studentkittens/eulenfunk/docs/paper/header.tex

\usepackage[autostyle=true,german=quotes]{csquotes}
\usepackage{graphicx}
\usepackage{lmodern}
\usepackage{hyperref}
\usepackage[utf8]{luainputenc}
\usepackage[T1]{fontenc}
\usepackage{gentium}
\usepackage{eurosym}
%\usepackage{pdfpages}
\pagenumbering{roman} 
\RequirePackage{ccicons}

\usepackage{inconsolata}
\usepackage{fancyhdr}
\usepackage{color}
\usepackage{amssymb}
\usepackage{wasysym}
%\definecolor{titlepagefontcolor}{RGB}{47, 90, 130} 
\definecolor{titlepagefontcolor}{RGB}{216,96,96}
\definecolor{titlepagefontcolorreset}{RGB}{255,255,255}
%\definecolor{titlepagecolor}{RGB}{55, 127, 161} 
%\definecolor{titlepagefontcolor}{RGB}{245,245,245} %Solarized light default text 
%\definecolor{titlepagefontcolor}{RGB}{55, 127, 161} 
%\definecolor{titlepagecolor}{RGB}{245,245,245} %Solarized light default text 
\definecolor{titlepagecolor}{RGB}{252,246,222}
\usepackage{ifthen}
\usepackage[usenames,dvipsnames]{xcolor}
\usepackage[
  paper=a4paper,
  left=30mm,
  right=25mm,
  top=25mm,
  bottom=25mm,
  includefoot,
  foot=\baselineskip,
  bindingoffset=0mm]{geometry}

\usepackage{setspace}
\onehalfspacing 

\usepackage{amssymb}% http://ctan.org/pkg/amssymb
\usepackage{pifont}% http://ctan.org/pkg/pifont
\newcommand{\cmark}{\textcolor{ForestGreen}{\ding{51}}}%
\newcommand{\xmark}{\textcolor{red}{\ding{55}}}%

\hypersetup{colorlinks,breaklinks,urlcolor=titlepagefontcolor,linkcolor=titlepagefontcolor}

\definecolor{gray75}{gray}{0.55}
\newcommand{\hsp}{\hspace{5pt}}

\usepackage{calc}
\usepackage{etoolbox}

\appto\chapterheadstartvskip{%
  \vspace{-7.7em} % Pull up chapter a bit.
  \smash{\makebox[0pt]{%
    \textcolor{titlepagefontcolor}{%
      \usesizeofkomafont{chapter}\rule[-2\ht\strutbox-\dp\strutbox]{2\paperwidth}{1.65\baselineskip}%
}}}}
\renewcommand\chapterformat{%
  \makebox[0pt][r]{\thechapter\ \ \textcolor{white}{\smash{\rule[-2\dp\strutbox]{2.5pt}{2.25\baselineskip}}}}%
  \enskip%
}

\addtokomafont{disposition}{\rmfamily}
\addtokomafont{chapter}{\color{titlepagecolor}}
\addtokomafont{section}{\color{titlepagefontcolor}}
\addtokomafont{subsection}{\color{titlepagefontcolor}}
\addtokomafont{subsubsection}{\color{titlepagefontcolor}}

\renewcommand{\labelitemi}{\textcolor{titlepagefontcolor}{$$$\blacktriangleright$}}
% \renewcommand{\labelitemii}{$\cdot$}
% \renewcommand{\labelitemiii}{$\diamond$}
% \renewcommand{\labelitemiv}{$\ast$}

\pagestyle{fancy}               

\newcommand{\prettypage}{%
    \scshape{~\thepage~~~}
}%

% Configure footer and header
\fancyfoot[C]{%
    % EasterEgg
    \ifthenelse{\value{page}=42}{%
        % Horizontal and vertical flip
        \reflectbox{\scalebox{1}[-1]{\prettypage}}
    }{%
        \ifthenelse{\value{page}=23}{%
            % Horizontal flip
            \reflectbox{\prettypage}
        }{%
            \prettypage
        }%
    }%
}%

% Remove the header from pages with chapters on them:
\fancypagestyle{plain}{%
    \fancyhead{}
    \renewcommand{\headrule}{}
}%

% \setlength{\headheight}{24pt} 

% Comment out for normal twoside:
% \newcommand{\ONESIDEFAKE}

\ifdefined\ONESIDEFAKE
    \fancyhead[L]{{\nouppercase{\slshape{\leftmark}}}}
    \fancyhead[R]{{\nouppercase{\scshape{\rightmark}}}}
\else
    \fancyhead[LO]{{\nouppercase{\slshape{\leftmark}}}}
    \fancyhead[RO]{{\nouppercase{\scshape{\rightmark}}}}
    \fancyhead[LE]{{\nouppercase{\scshape{\rightmark}}}}
    \fancyhead[RE]{{\nouppercase{\slshape{\leftmark}}}}
\fi

%\setlength{\topmargin}{-.5in}  %{-.5625in}
\setlength{\footskip}{25pt} % to put page number 3/4" from the bottom of the page (1/4" from bottom of body text)
%\setlength{\textheight}{9in}
%\setlength{\textwidth}{6in}
\usepackage[
    type={CC},
    modifier={by-nc-sa},
    version={3.0},
]{doclicense}
