studentkittens/eulenfunk/docs/paper/images/about.png

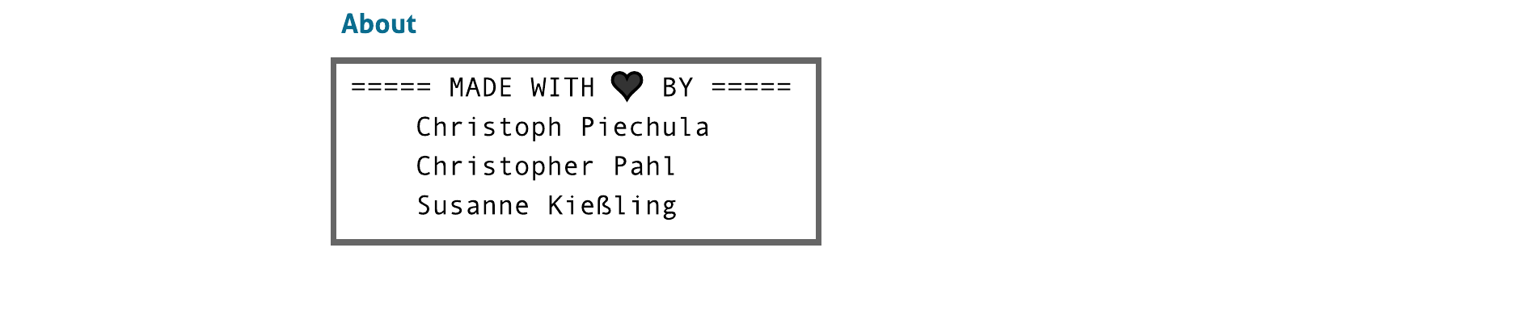
docs/paper/images/about.png
