studentkittens/eulenfunk/docs/paper/images/back_1.png

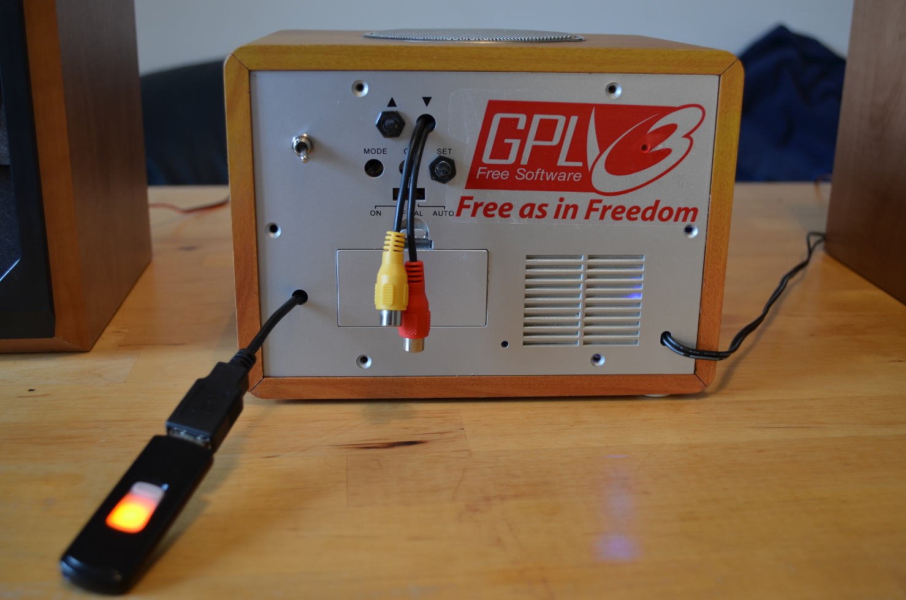
docs/paper/images/back_1.png
