studentkittens/eulenfunk/docs/paper/images/clock.png

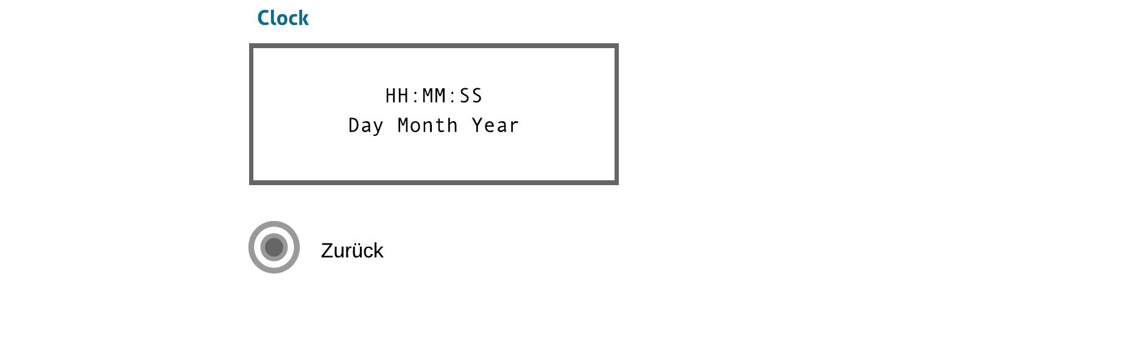
docs/paper/images/clock.png
