studentkittens/eulenfunk/docs/paper/images/currentsong.png

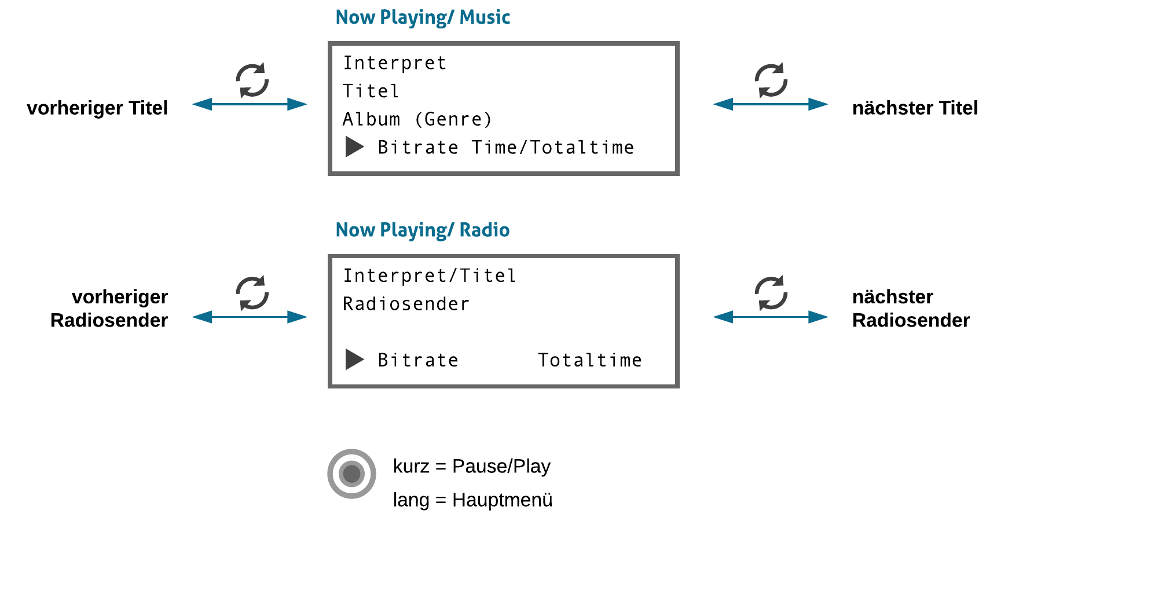
docs/paper/images/currentsong.png
