studentkittens/eulenfunk/docs/paper/images/encoding.png

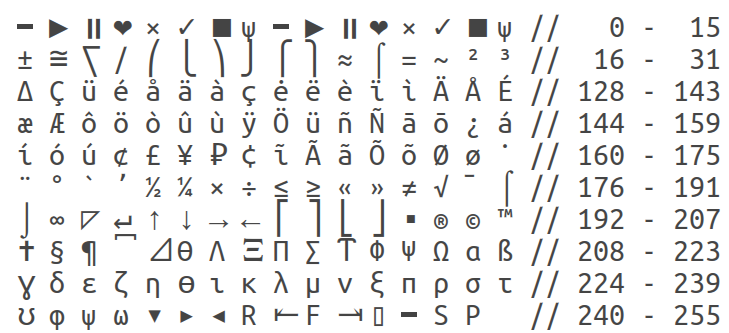
docs/paper/images/encoding.png
