studentkittens/eulenfunk/docs/paper/images/eulenfunk-ambilight.png

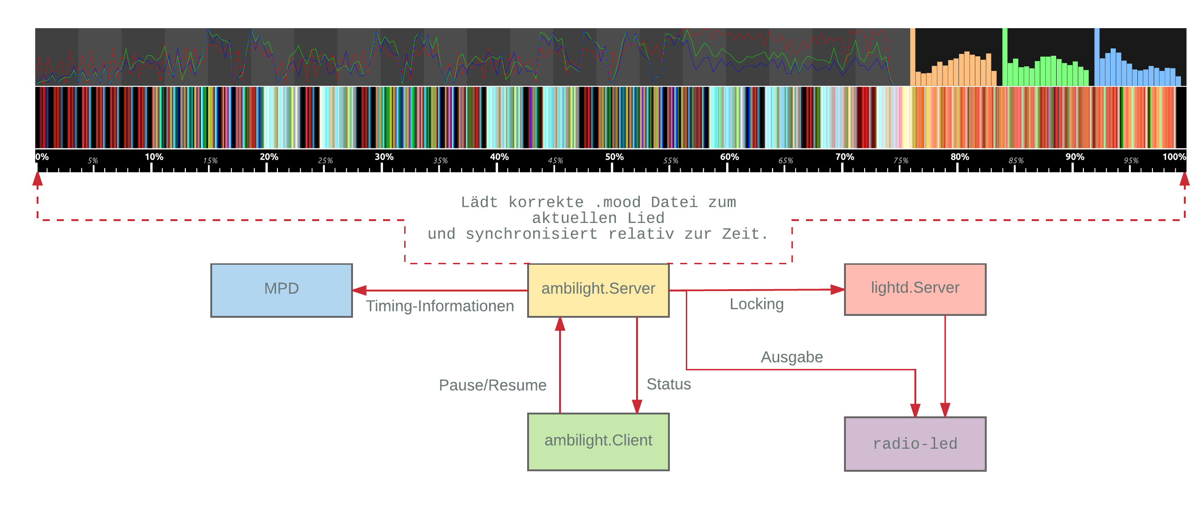
docs/paper/images/eulenfunk-ambilight.png
