studentkittens/eulenfunk/docs/paper/images/eulenfunk-automount.png

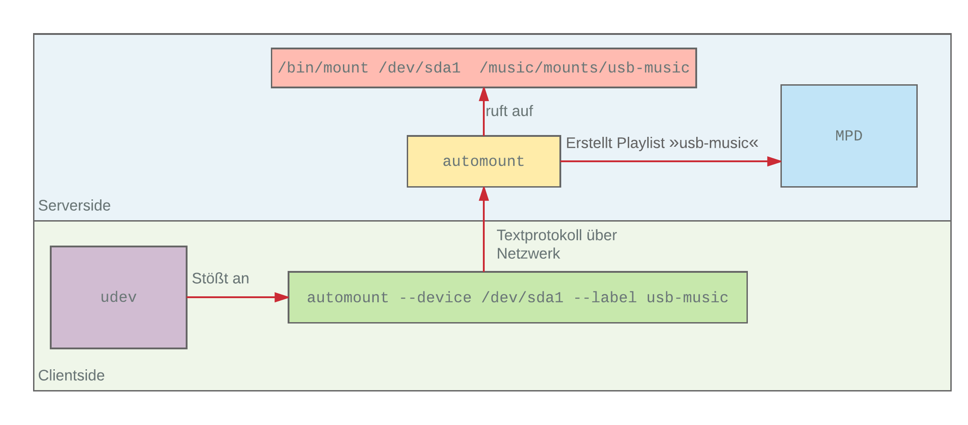
docs/paper/images/eulenfunk-automount.png
