studentkittens/eulenfunk/docs/paper/images/eulenfunk-pwm.png

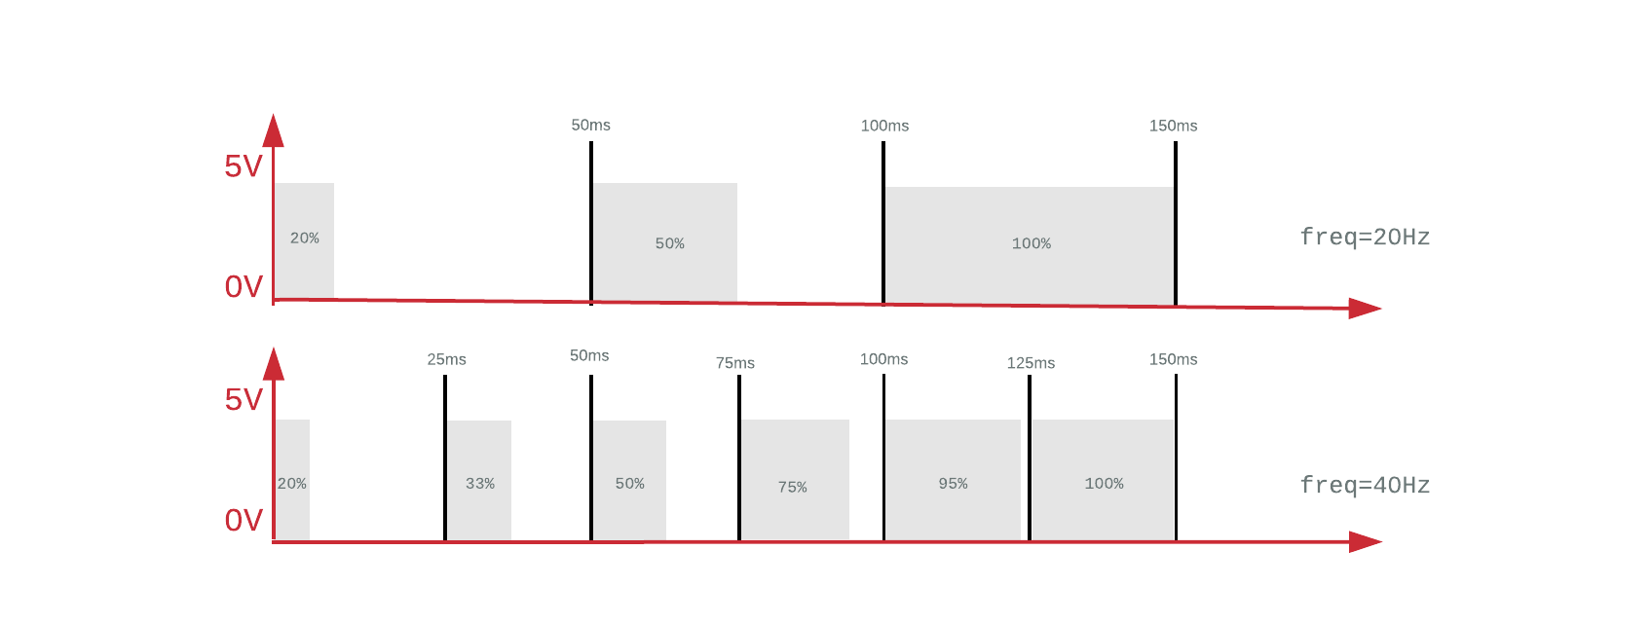
docs/paper/images/eulenfunk-pwm.png
