studentkittens/eulenfunk/docs/paper/images/eulenfunk-services.png

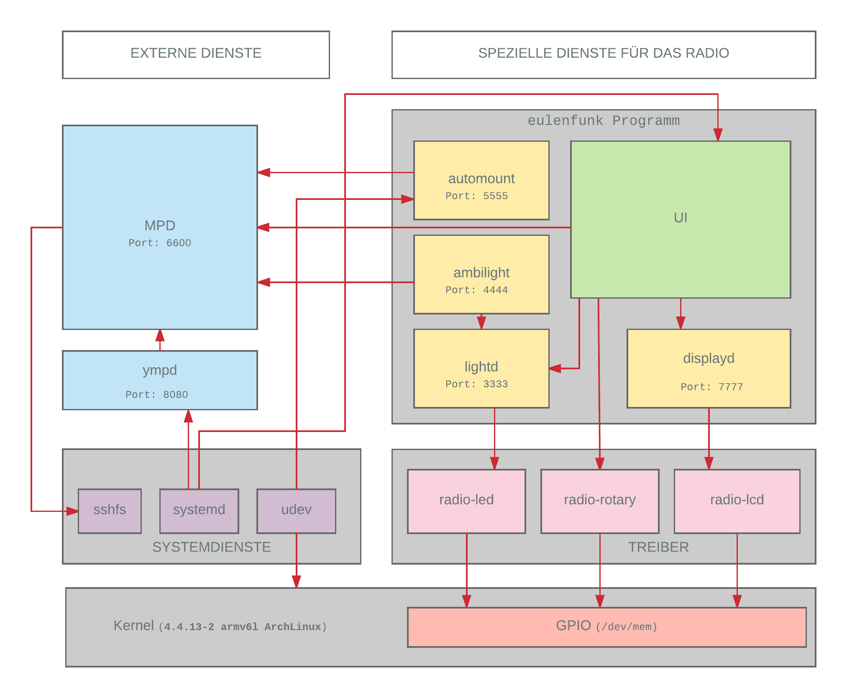
docs/paper/images/eulenfunk-services.png
