studentkittens/eulenfunk/docs/paper/images/eulenfunk-systemd.png

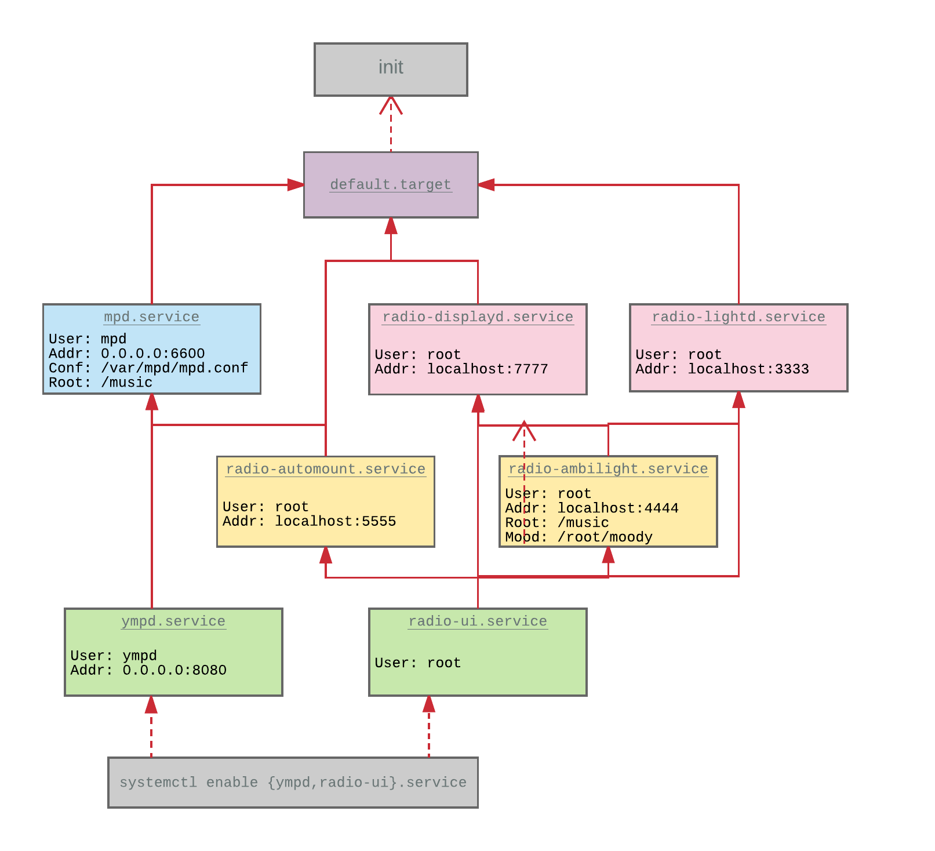
docs/paper/images/eulenfunk-systemd.png
