studentkittens/eulenfunk/docs/paper/images/eulenfunk-ui.png

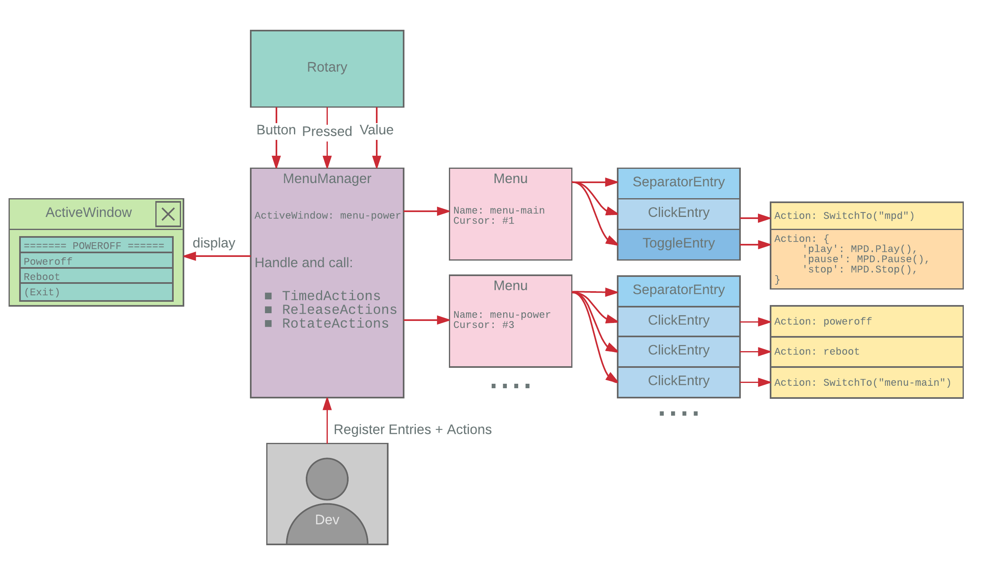
docs/paper/images/eulenfunk-ui.png
