studentkittens/eulenfunk/docs/paper/images/eulenfunk.jpg

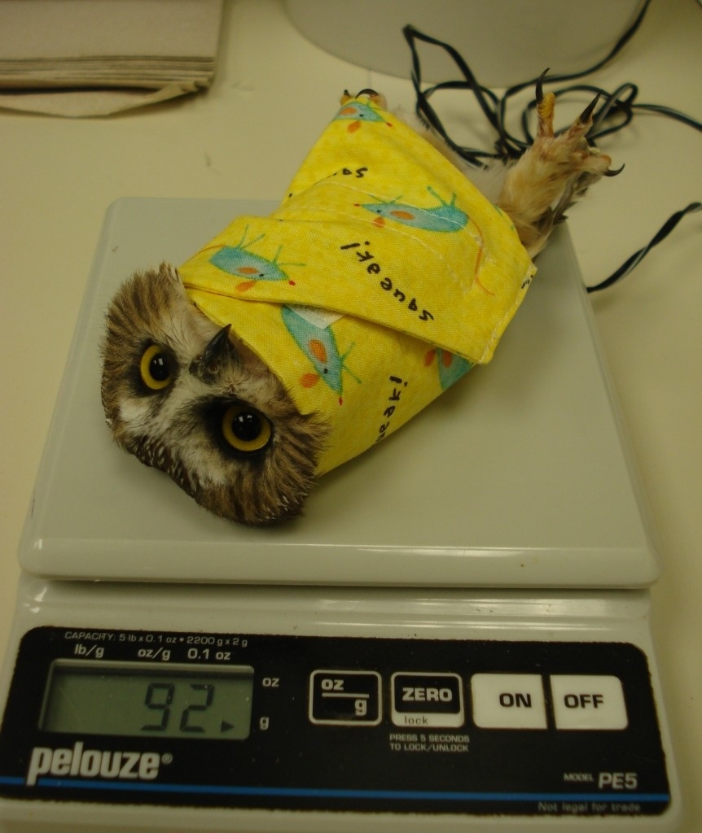
docs/paper/images/eulenfunk.jpg
