studentkittens/eulenfunk/docs/paper/images/eulenfunk.png

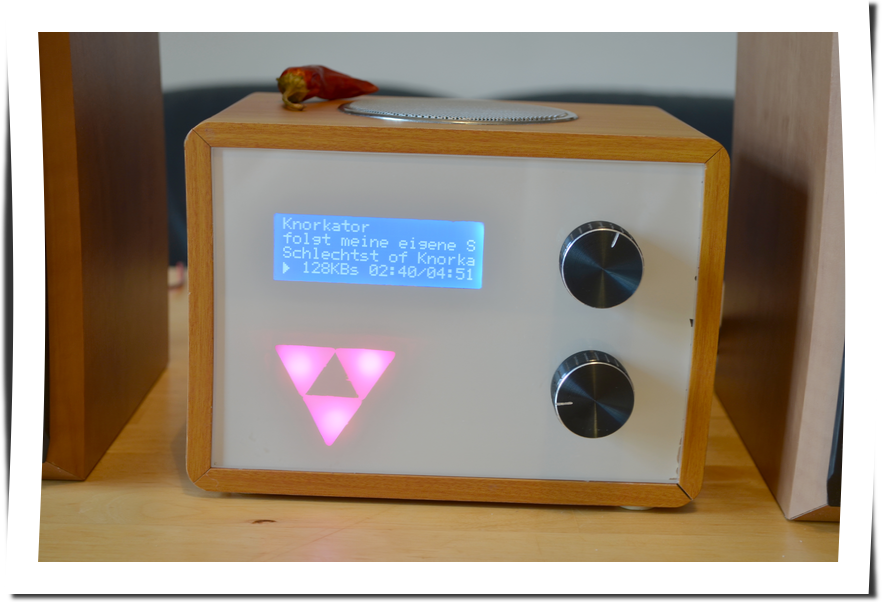
docs/paper/images/eulenfunk.png
