studentkittens/eulenfunk/docs/paper/images/eulenfunksh.png

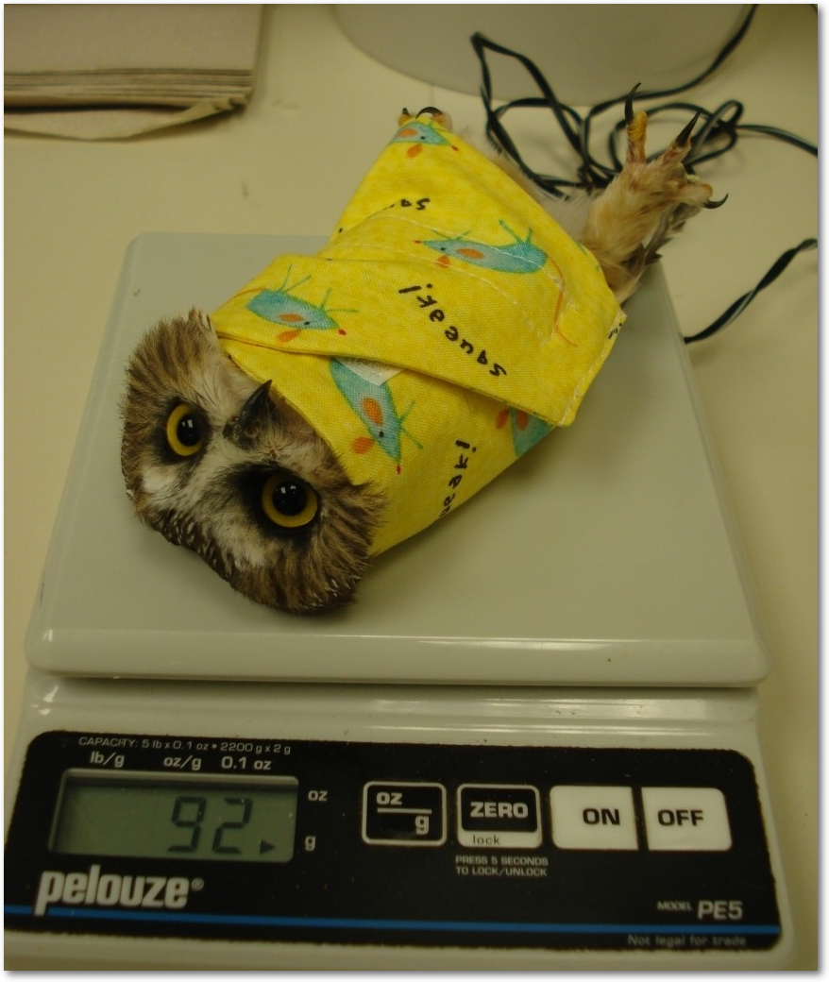
docs/paper/images/eulenfunksh.png
