studentkittens/eulenfunk/docs/paper/images/front_1.png

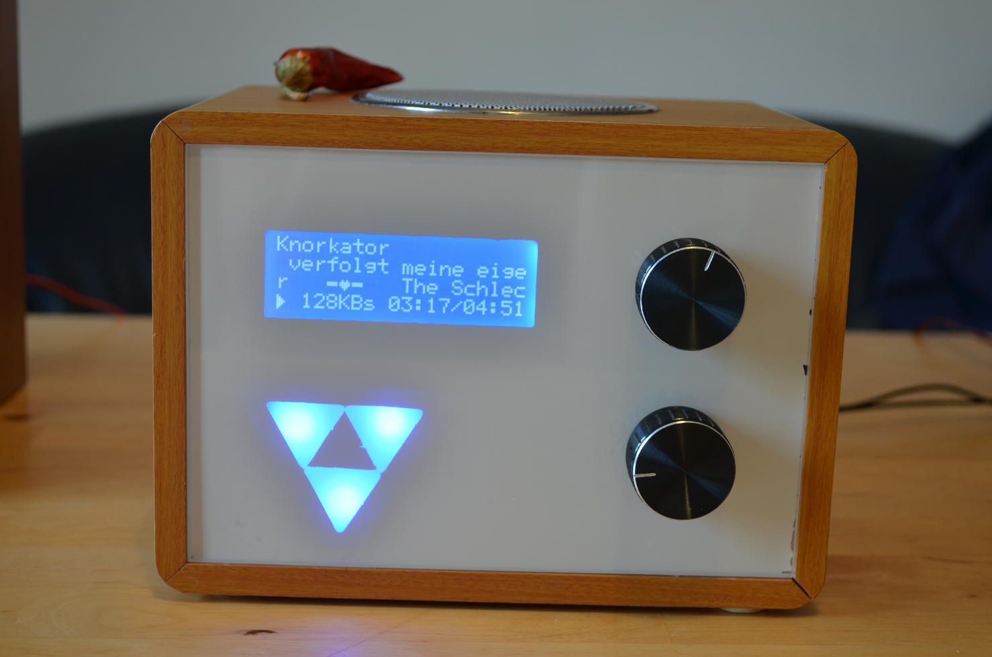
docs/paper/images/front_1.png
