studentkittens/eulenfunk/docs/paper/images/front_3.png

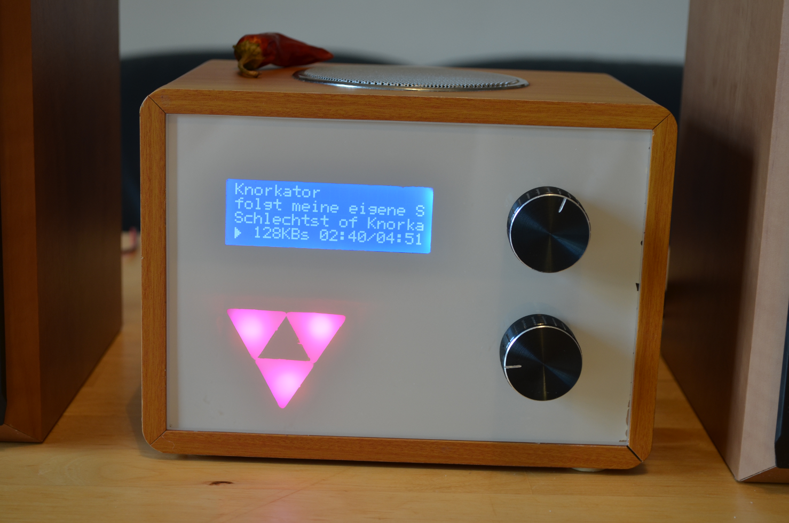
docs/paper/images/front_3.png
