studentkittens/eulenfunk/docs/paper/images/lcdraspi.png

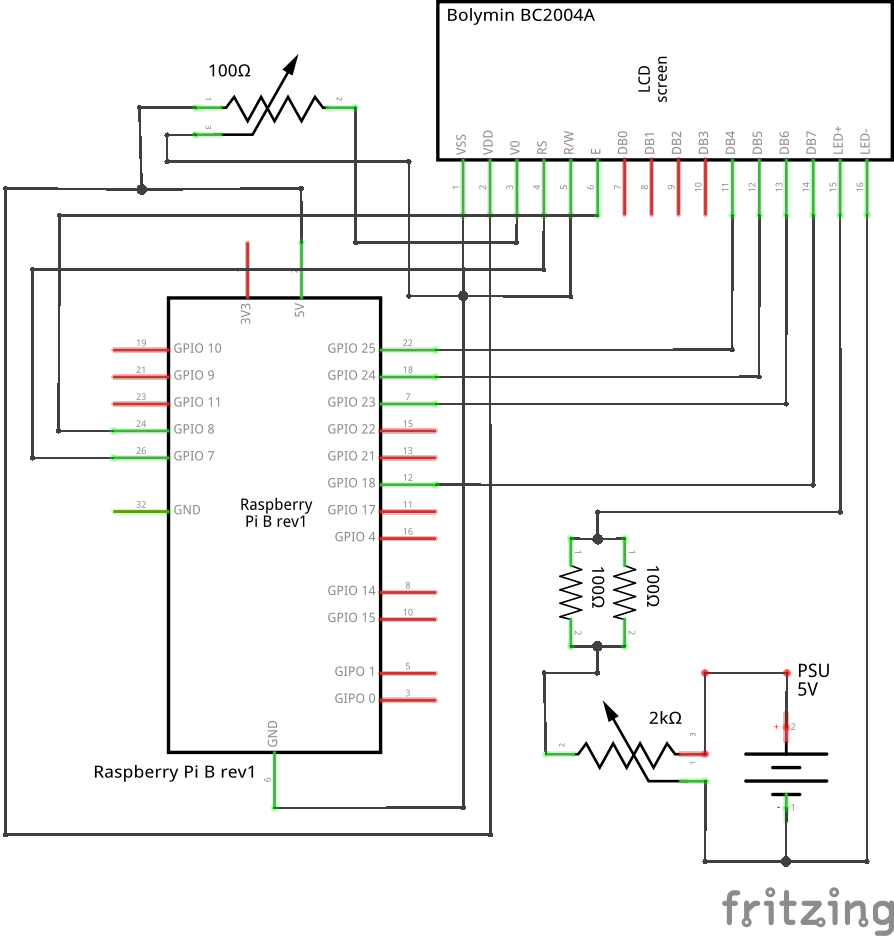
docs/paper/images/lcdraspi.png
