studentkittens/eulenfunk/docs/paper/images/led.png

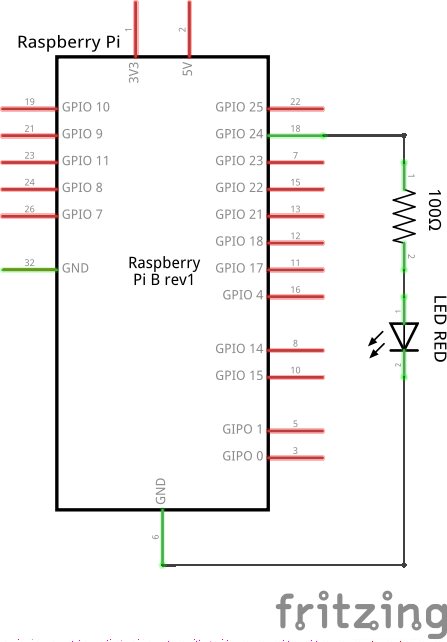
docs/paper/images/led.png
