studentkittens/eulenfunk/docs/paper/images/mpd-overview.png

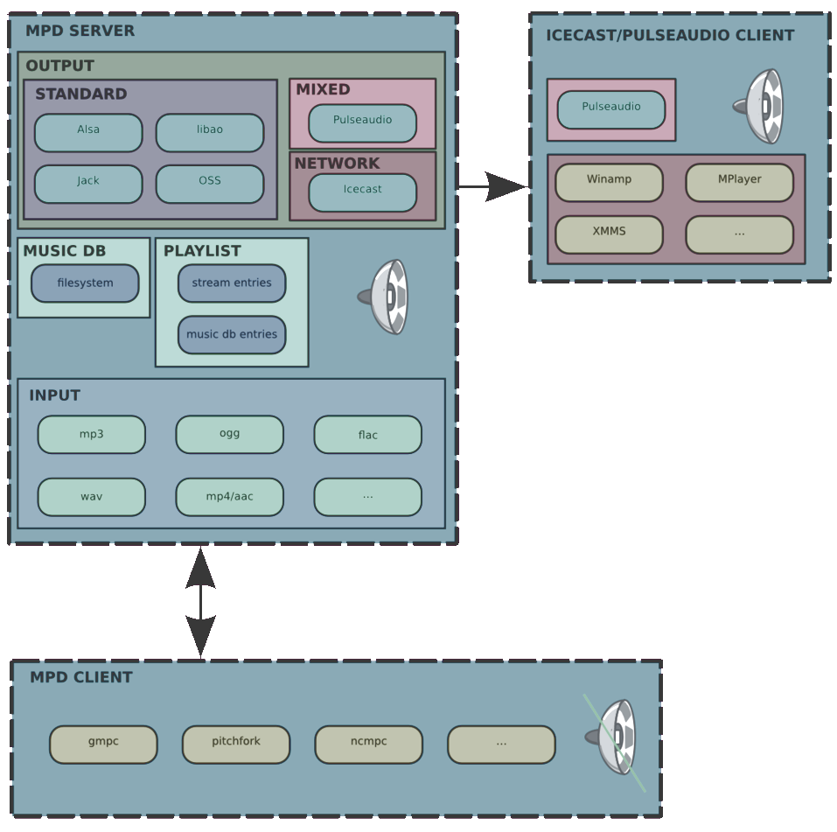
docs/paper/images/mpd-overview.png
