studentkittens/eulenfunk/docs/paper/images/options.png

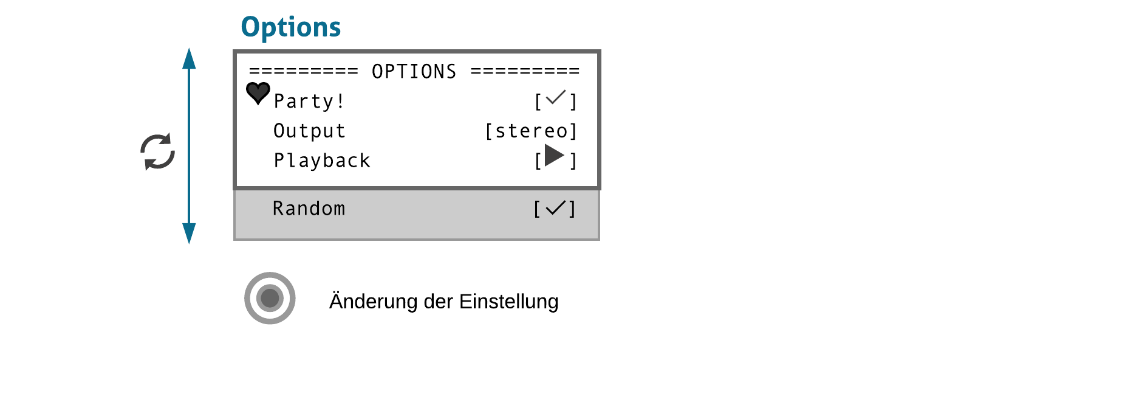
docs/paper/images/options.png
