studentkittens/eulenfunk/docs/paper/images/powermenu.png

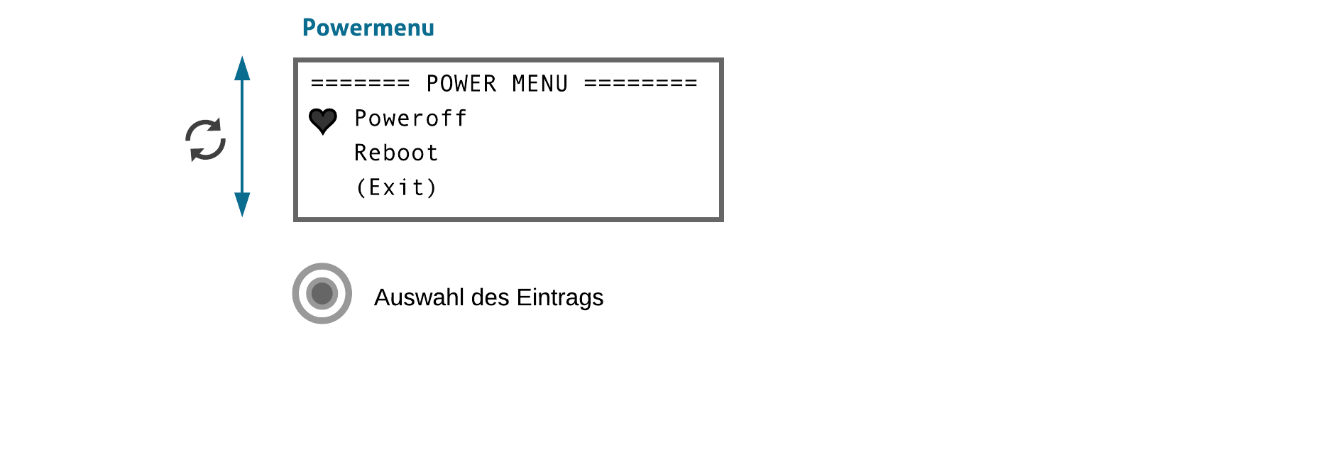
docs/paper/images/powermenu.png
