studentkittens/eulenfunk/docs/paper/images/ral_soft.png

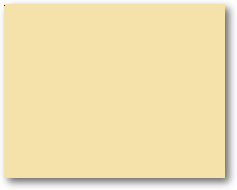
docs/paper/images/ral_soft.png
