studentkittens/eulenfunk/docs/paper/images/rotary.png

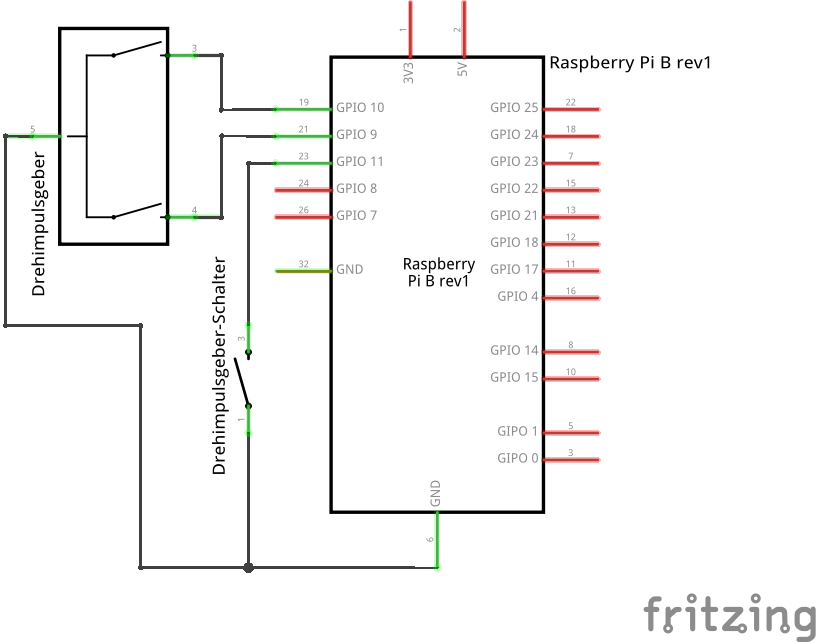
docs/paper/images/rotary.png
