studentkittens/eulenfunk/docs/paper/images/rotary_soft.png

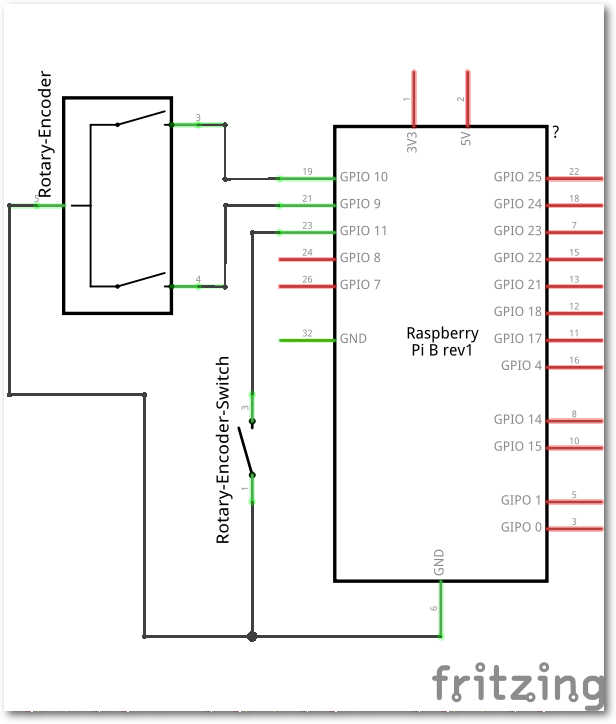
docs/paper/images/rotary_soft.png
