studentkittens/eulenfunk/docs/paper/images/snobaer-small.png

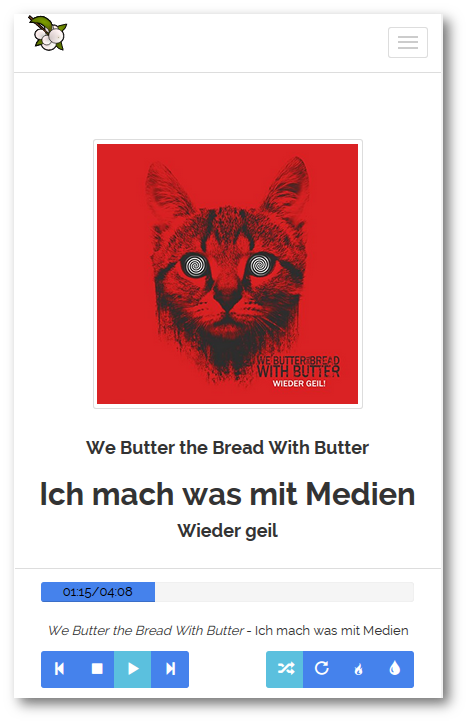
docs/paper/images/snobaer-small.png
