studentkittens/eulenfunk/docs/paper/images/statistics.png

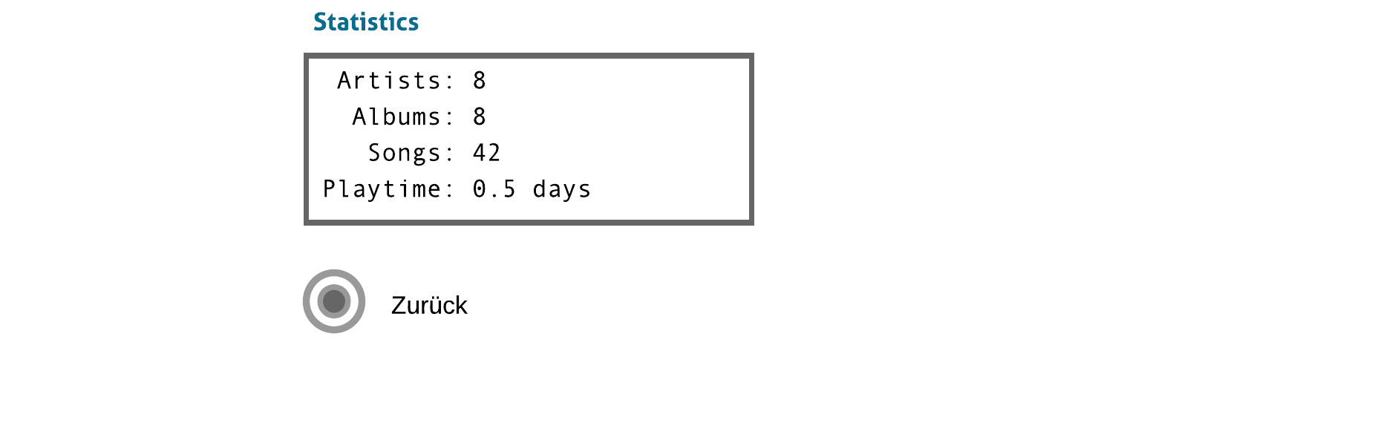
docs/paper/images/statistics.png
