studentkittens/eulenfunk/docs/paper/images/symbols.png

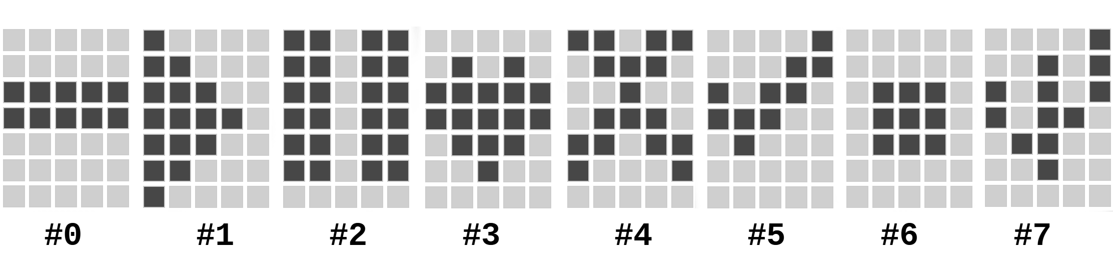
docs/paper/images/symbols.png
