studentkittens/eulenfunk/docs/paper/images/symbols/check.png

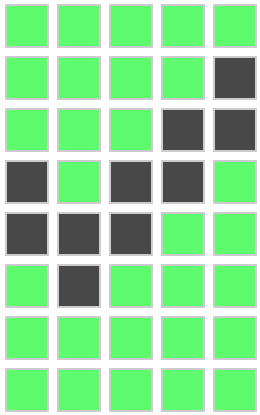
docs/paper/images/symbols/check.png
