studentkittens/eulenfunk/docs/paper/images/symbols/cross.png

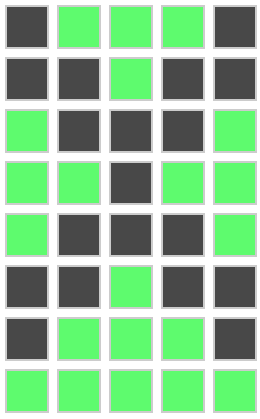
docs/paper/images/symbols/cross.png
