studentkittens/eulenfunk/docs/paper/images/symbols/gb.png

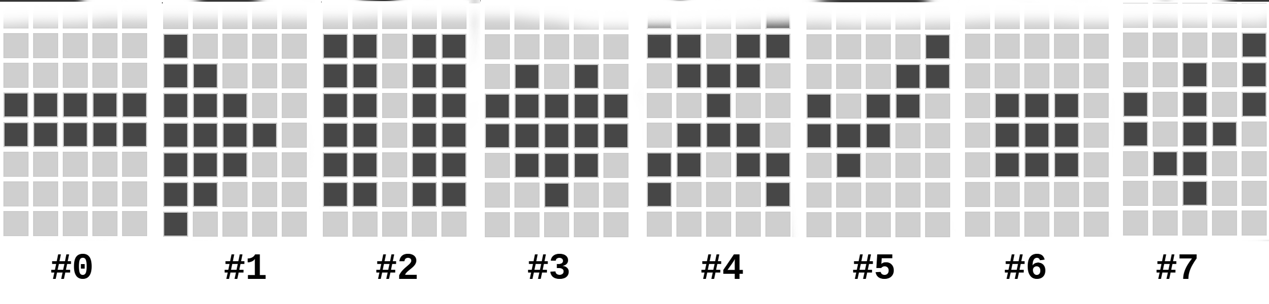
docs/paper/images/symbols/gb.png
