studentkittens/eulenfunk/docs/paper/images/symbols/hbar.png

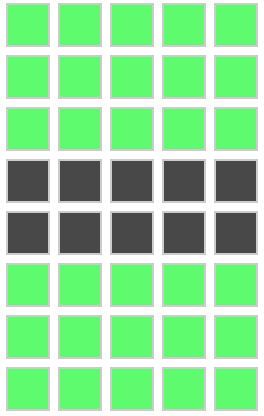
docs/paper/images/symbols/hbar.png
