studentkittens/eulenfunk/docs/paper/images/symbols/heart.png

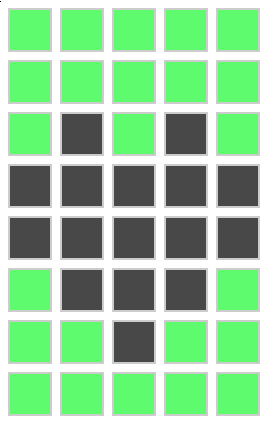
docs/paper/images/symbols/heart.png
