studentkittens/eulenfunk/docs/paper/images/symbols/pause.png

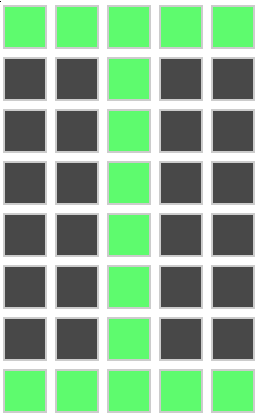
docs/paper/images/symbols/pause.png
