studentkittens/eulenfunk/docs/paper/images/symbols/play.png

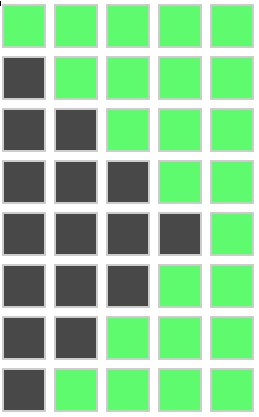
docs/paper/images/symbols/play.png
