studentkittens/eulenfunk/docs/paper/images/systeminfo.png

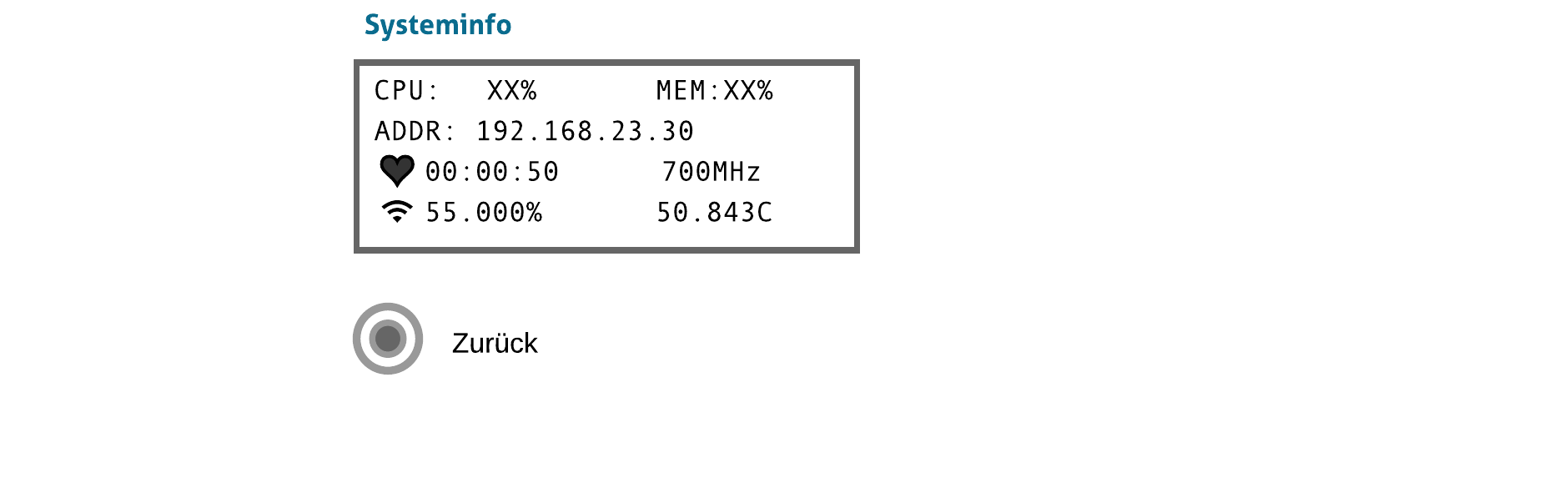
docs/paper/images/systeminfo.png
