studentkittens/eulenfunk/docs/paper/images/ympd.png

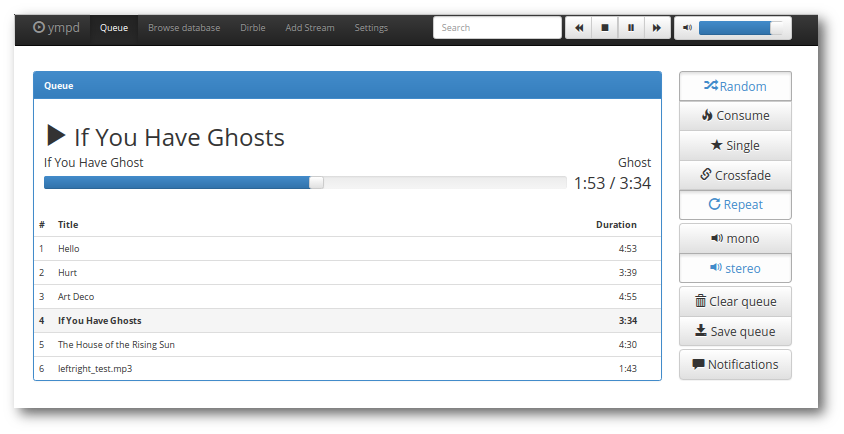
docs/paper/images/ympd.png
