studentkittens/eulenfunk/docs/slides/images/poloroid.png

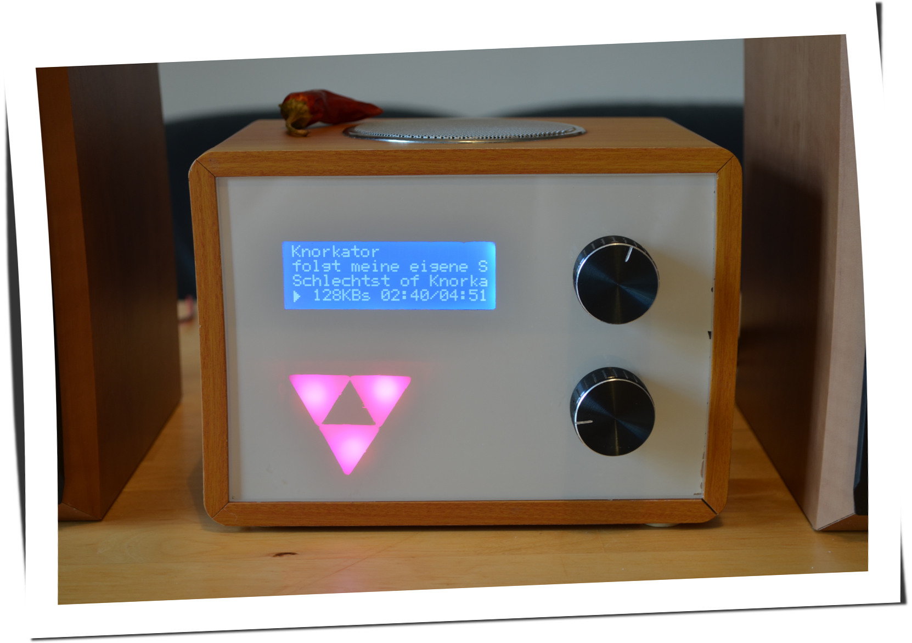
docs/slides/images/poloroid.png
