studentkittens/eulenfunk/docs/paper/images/front_usage.png

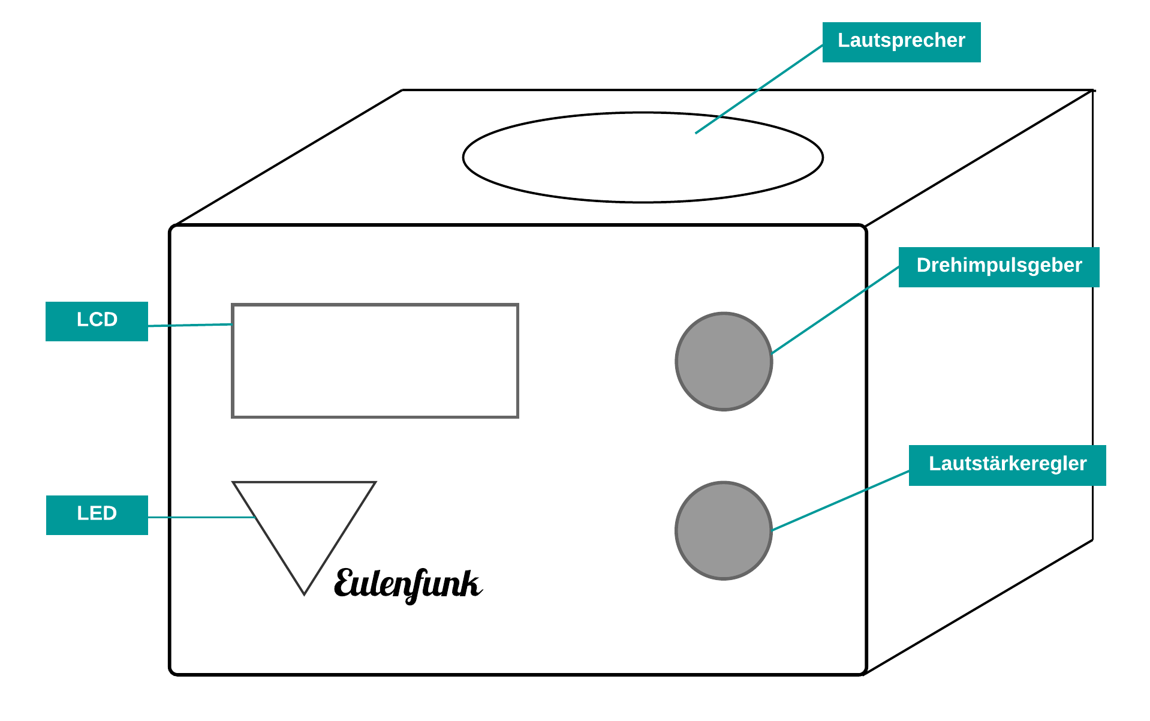
docs/paper/images/front_usage.png
